herraa1/msx-joypc-v1/firmware/msx-joypc-v1/GamePort.h

// This file is part of Necroware's GamePort adapter firmware.
// Copyright (C) 2021 Necroware
//
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
#pragma once

// Simple GamePort pins to Arduino pins mapper.
// GamePort pins <1>, <8>, <9> are already connected to "VCC" via the PCB
template <int I>
struct GamePort {
  enum { pin = -1 };
};

// Analog: Button #1
// Digital (e.g. SW3D): Clock
template <>
struct GamePort<2> {
  enum { pin = 10 };
};

// Analog: Joystick1 X-Axis 
// Digital (e.g. SW3D): Trigger
template <>
struct GamePort<3> {
  enum { pin = A0 };
};

// Analog: Joystick1 Y-Axis 
template <>
struct GamePort<6> {
  enum { pin = A4 };
};

// Analog: Button #2
// Digital (e.g. SW3D): Data 0
template <>
struct GamePort<7> {
  enum { pin = 8 };
};

// Analog: Button #3
// Digital (e.g. SW3D): Data 1
template <>
struct GamePort<10> {
  enum { pin = A5 };
};

// Analog: Joystick2 X-Axis 
template <>
struct GamePort<11> {
  enum { pin = 7 };
};

// Analog: Midi OUT
//template <>
//struct GamePort<12> {
//  enum { pin = 5 };
//};

// Analog: Joystick2 Y-Axis 
template <>
struct GamePort<13> {
  enum { pin = 6 };
};

// Analog: Button #4
// Digital (e.g. SW3D): Data 2
template <>
struct GamePort<14> {
  enum { pin = 9 };
};

// Analog: Midi IN
//template <>
//struct GamePort<15> {
//  enum { pin = 9 };
//};
